Christian-TUM-Makerspace/Tissue-Culture-Rotator_-_repair-and-OD_measuring/images/Project 2.jpg

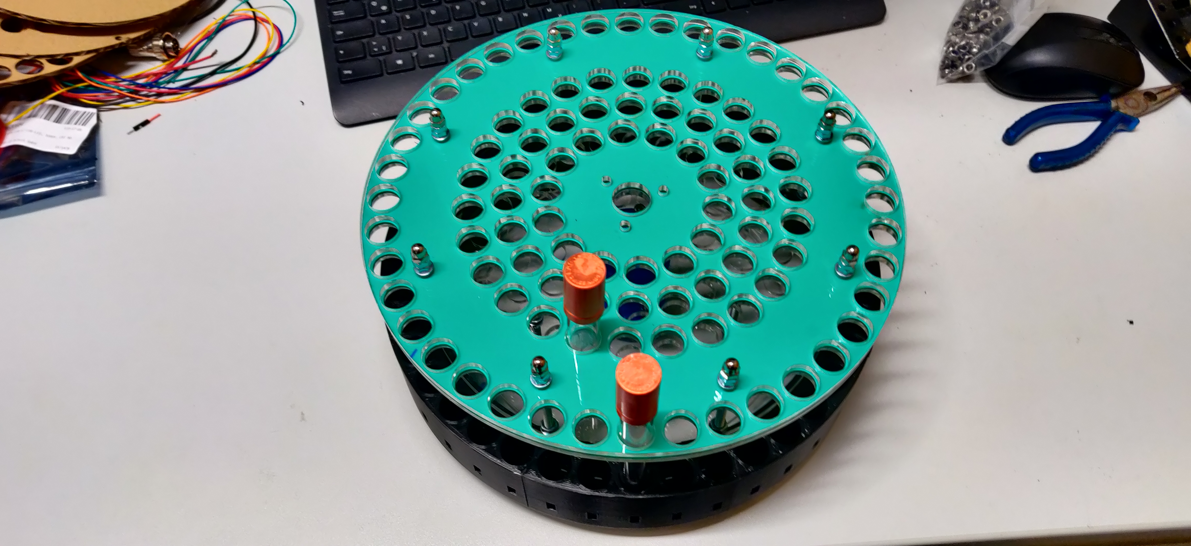
images/Project 2.jpg
