Christian-TUM-Makerspace/Tissue-Culture-Rotator_-_repair-and-OD_measuring/program/images/Stop mode.png

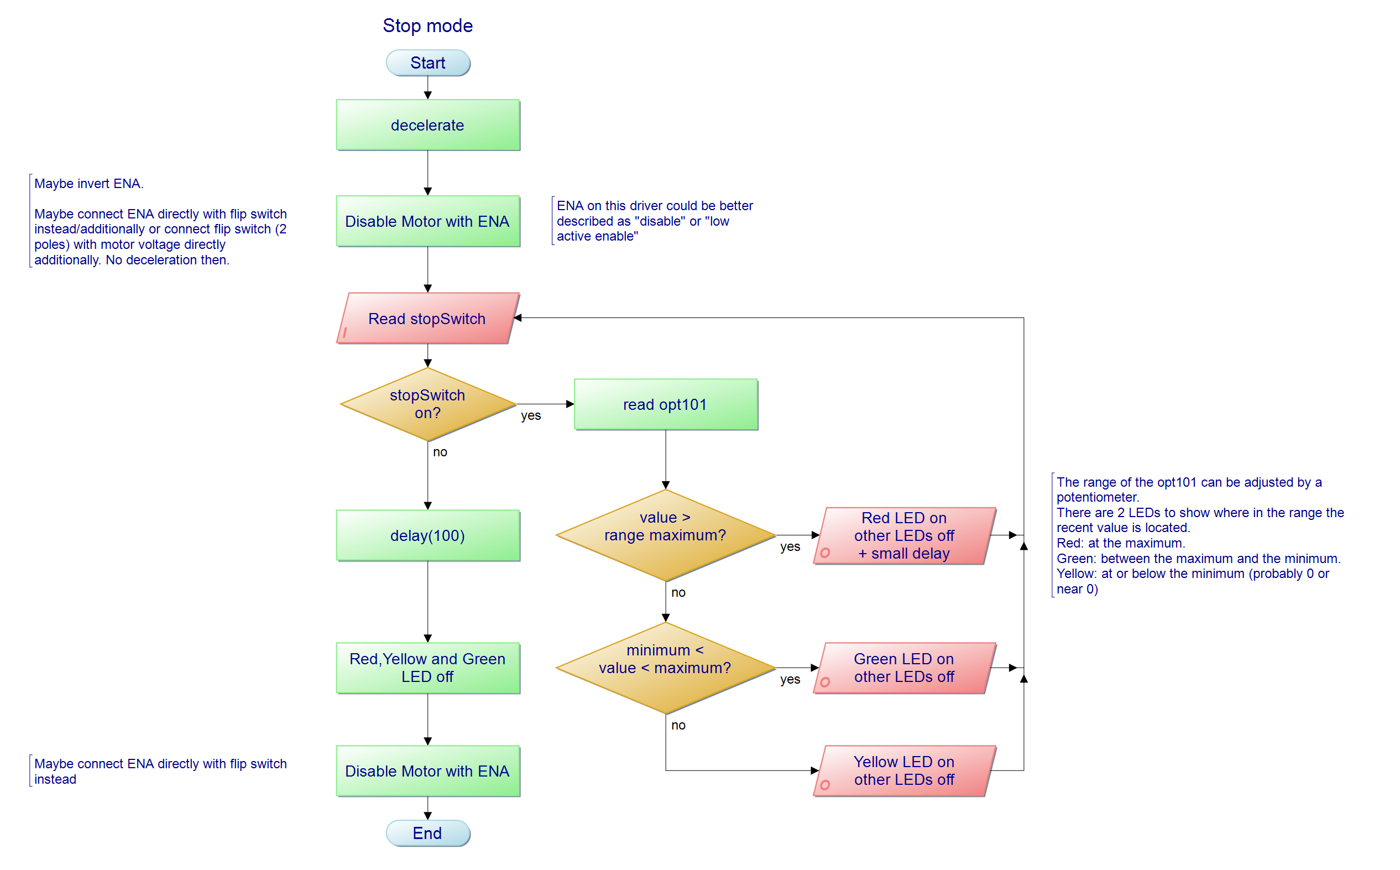
program/images/Stop mode.png
