Christian-TUM-Makerspace/Tissue-Culture-Rotator_-_repair-and-OD_measuring/program/images/Measure revolution.png

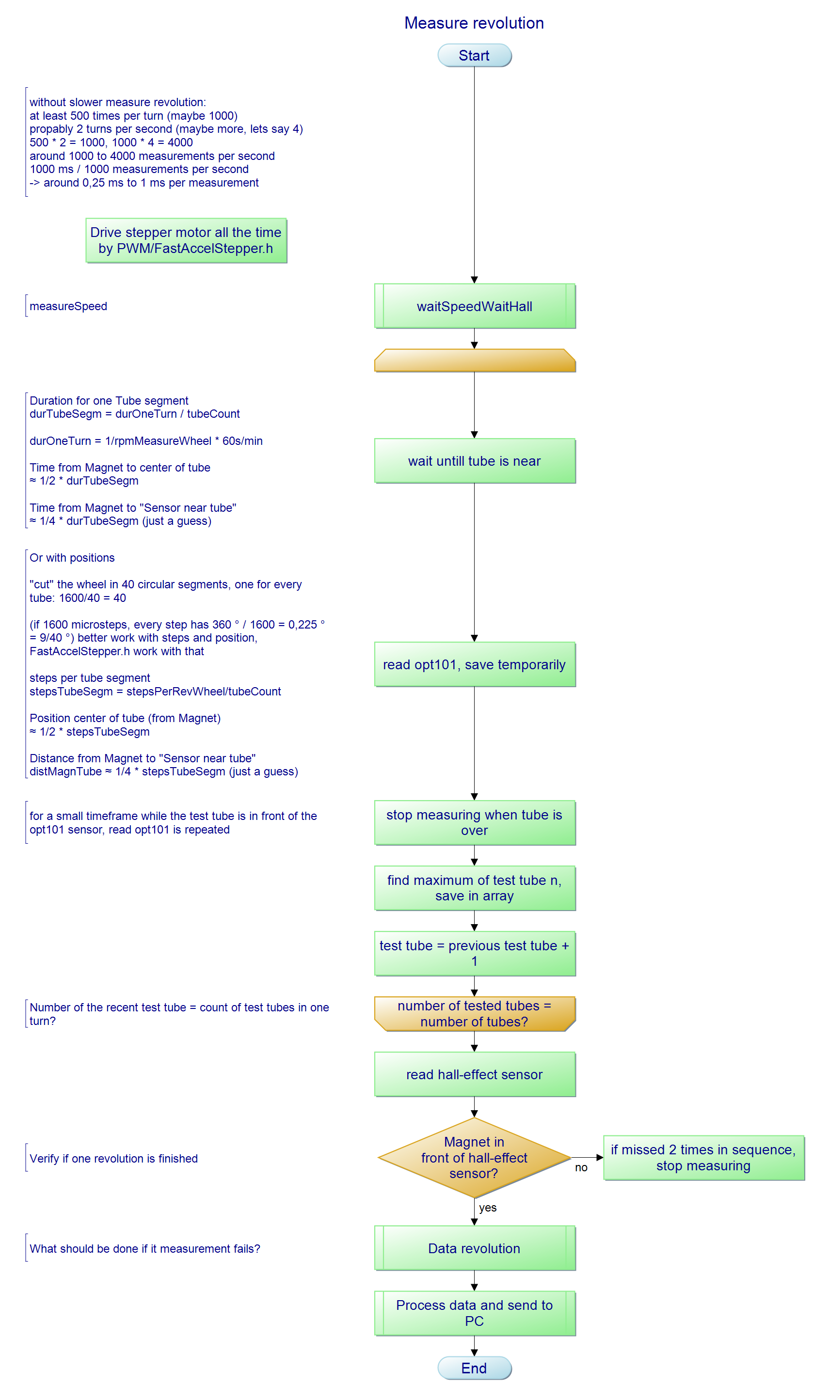
program/images/Measure revolution.png
