Christian-TUM-Makerspace/Tissue-Culture-Rotator_-_repair-and-OD_measuring/testcode/Hall_Sensor_KY-024.ino

#define hallSensor 35

int hallVal = 0;

void setup() {
  Serial.begin(115200);
  pinMode(hallSensor, INPUT);

}

void loop() {
  hallVal = analogRead(hallSensor);
  Serial.println(hallVal);
  delay(100);

}
